antoniolosada/MEIGA/DOC/20240906_141103.jpg

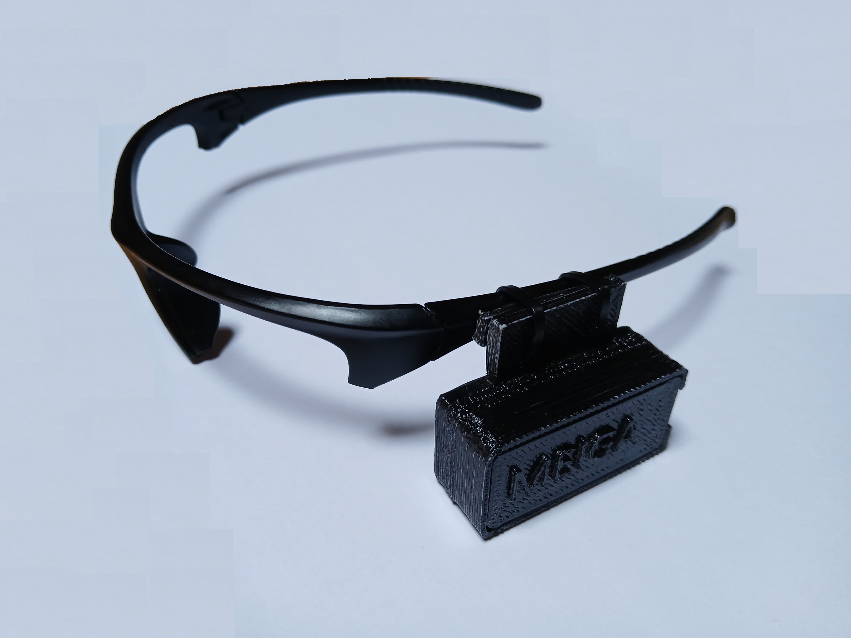
DOC/20240906_141103.jpg
