antoniolosada/MEIGA/DOC/ESP32C3_MPU6050_FPC9T2XLS634A4O.webp

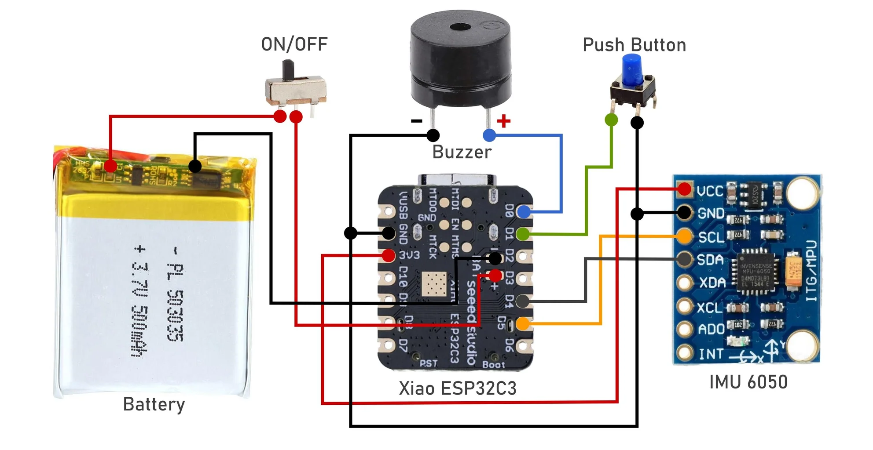
DOC/ESP32C3_MPU6050_FPC9T2XLS634A4O.webp
