antoniolosada/MEIGA/DOC/HTB1TN.CHpXXXXXGaXXXq6xXFXXXe.webp

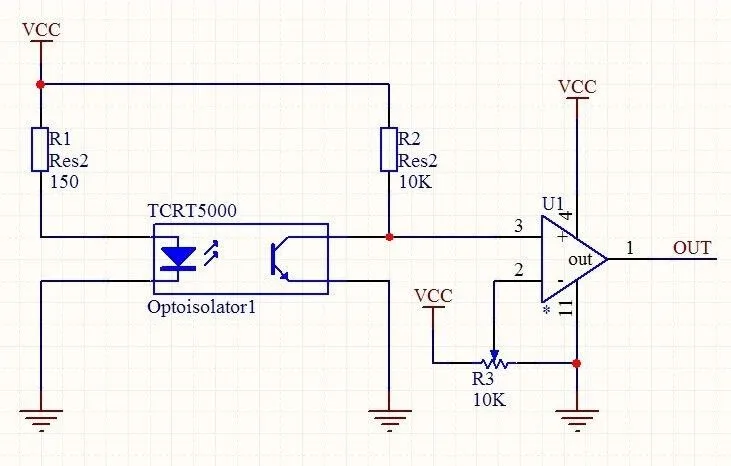
DOC/HTB1TN.CHpXXXXXGaXXXq6xXFXXXe.webp
