antoniolosada/MEIGA/DOC/MEiga.bmp

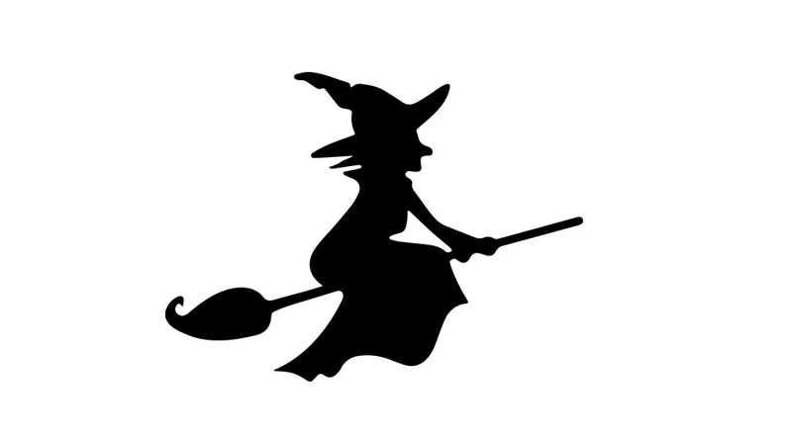
DOC/MEiga.bmp
