antoniolosada/MEIGA/DOC/MEIGA_CFG.png

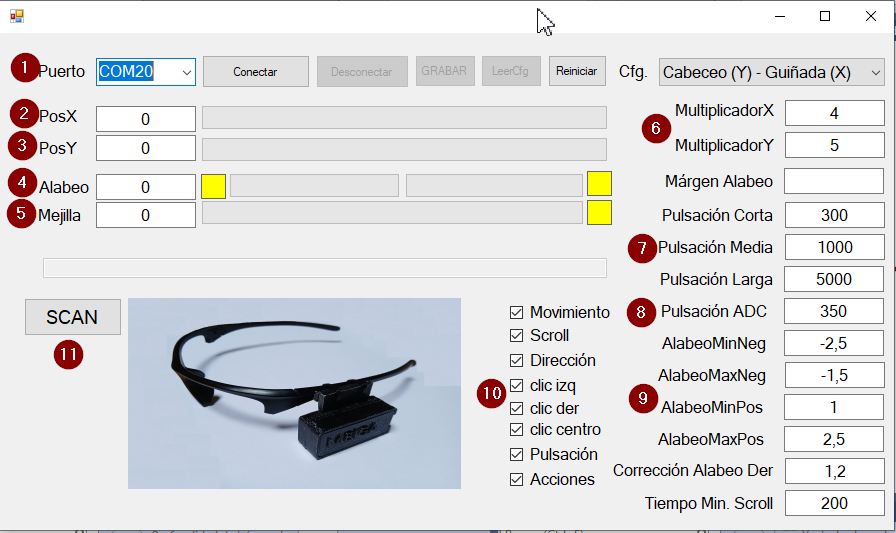
DOC/MEIGA_CFG.png
