antoniolosada/MEIGA/DOC/Seeed-Studio-XIAO-ESP32S3-2-4GHz-Wi-Fi-Bluetooth-BLE-5-0-Dual-Core-Development-Board.webp

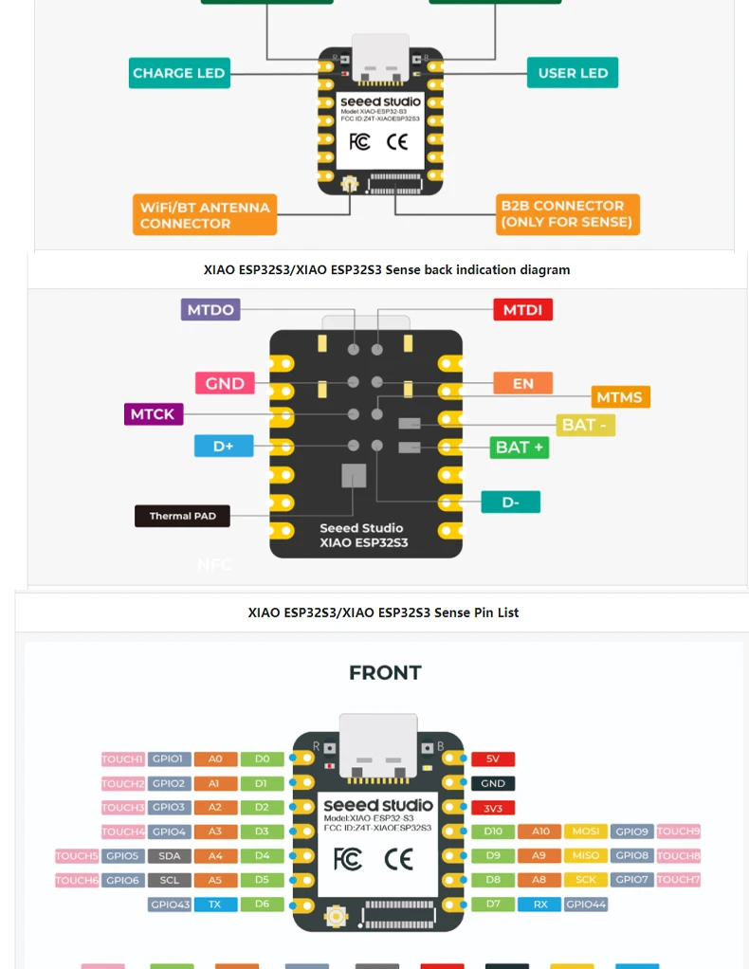
DOC/Seeed-Studio-XIAO-ESP32S3-2-4GHz-Wi-Fi-Bluetooth-BLE-5-0-Dual-Core-Development-Board.webp
