antoniolosada/MEIGA/DOC/TCRT5000.webp

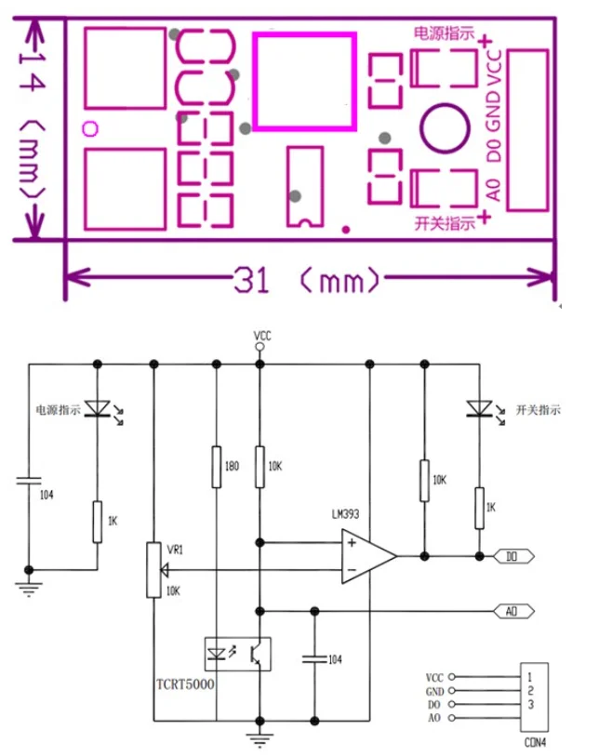
DOC/TCRT5000.webp
