antoniolosada/MEIGA/FreeCad/caja.png

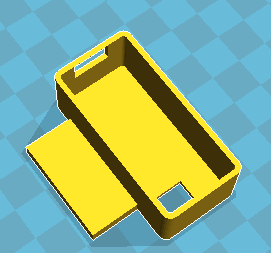
FreeCad/caja.png
