antoniolosada/MEIGA/FreeCad/tapa.png

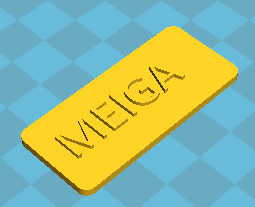
FreeCad/tapa.png
